msolajic/c64-uni-cart/images/pcb_artwork.png

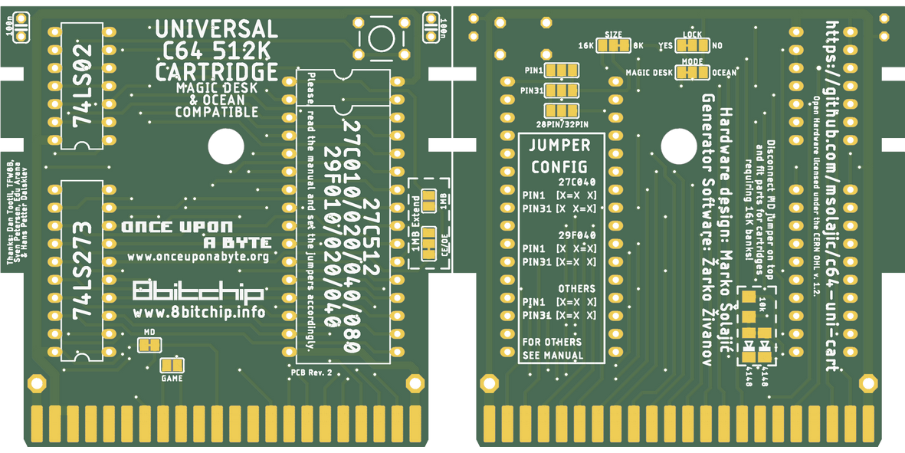
images/pcb_artwork.png
